broedschroed/NeoChristmasTreeV2/docs/Bilder/20261003_232223.jpg

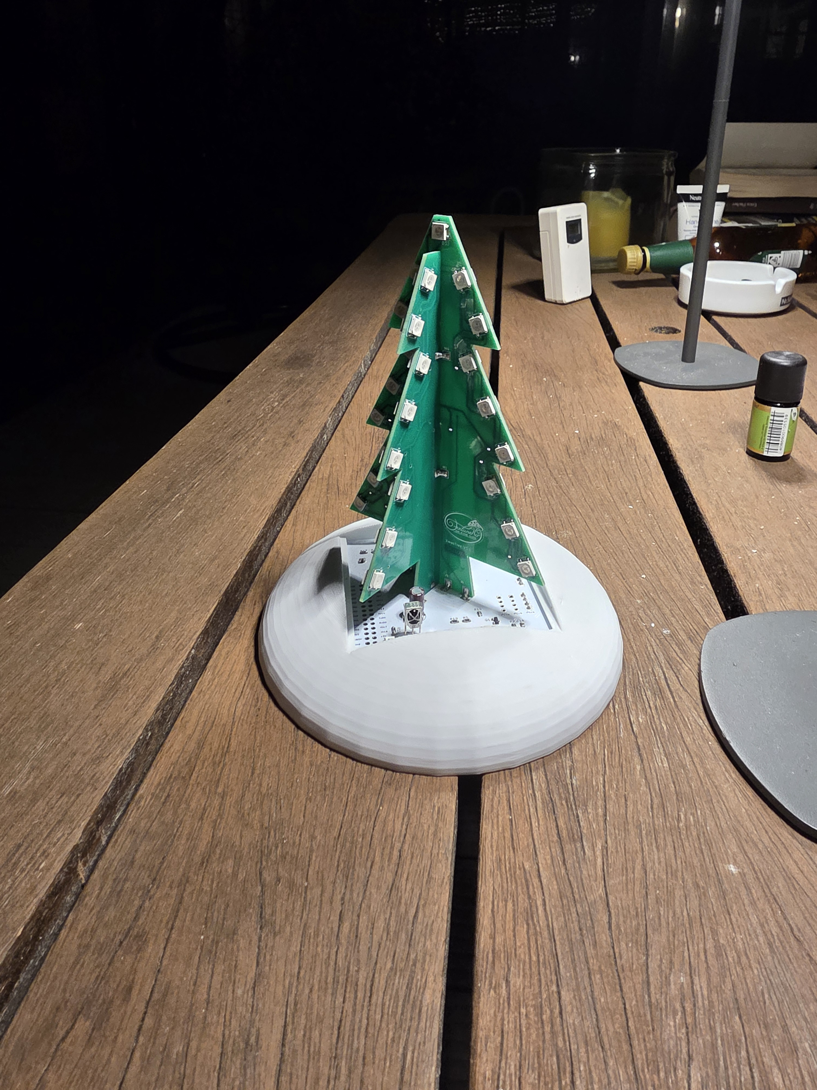
docs/Bilder/20261003_232223.jpg
