broedschroed/NeoChristmasTreeV2/docs/Bilder/20261003_232228.jpg

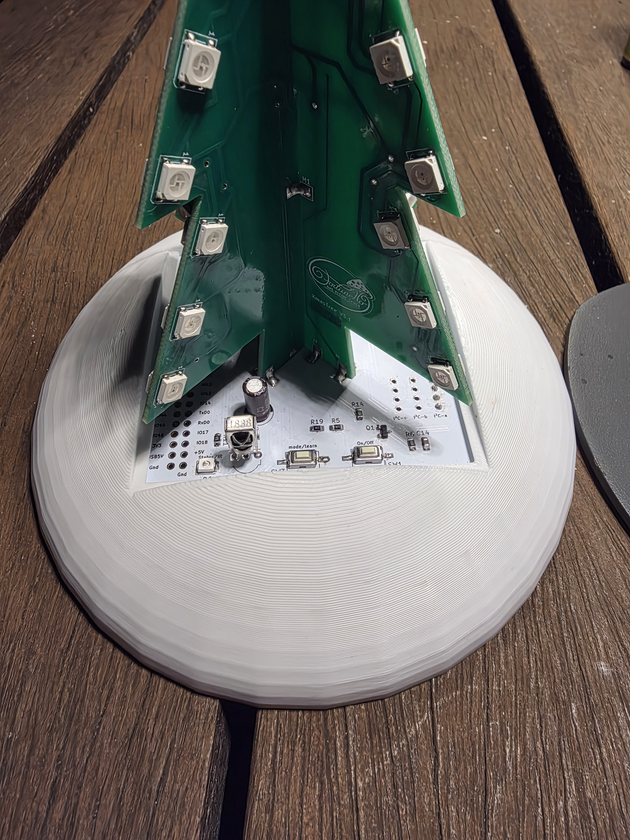
docs/Bilder/20261003_232228.jpg
