broedschroed/NeoChristmasTreeV2/docs/Bilder/20261003_232233.jpg

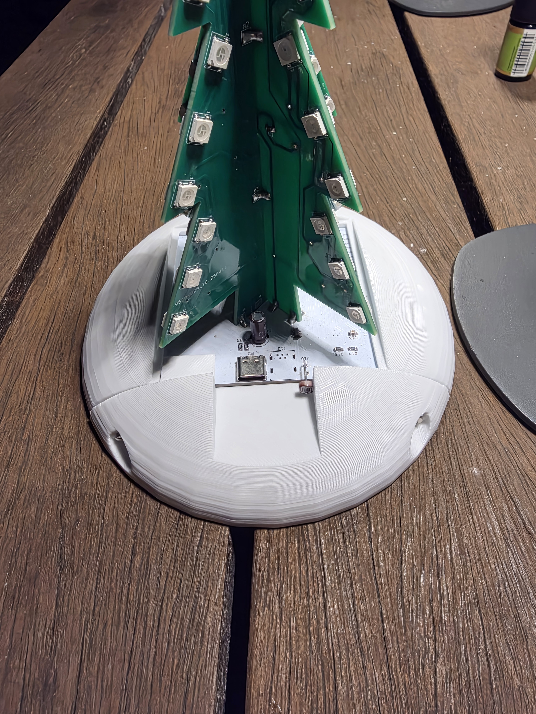
docs/Bilder/20261003_232233.jpg
