broedschroed/NeoChristmasTreeV2/docs/Bilder/20261003_232258.jpg

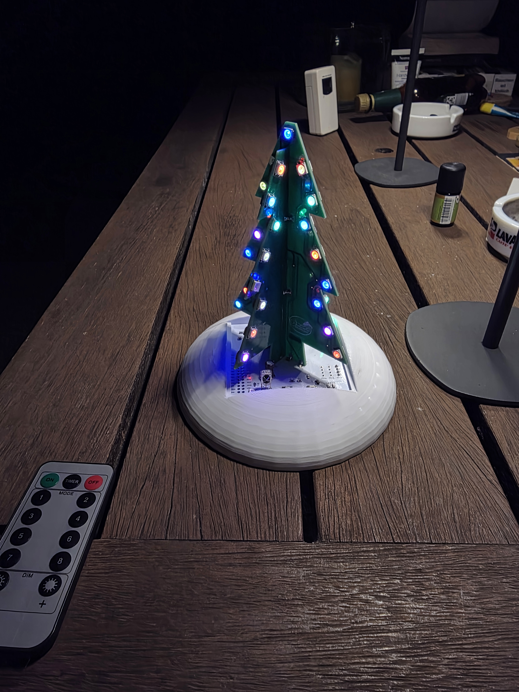
docs/Bilder/20261003_232258.jpg
