broedschroed/NeoChristmasTreeV2/IRcodes.h

#define MAXIRCODES 13

unsigned int defaultIRcodes [MAXIRCODES] = {
  0xFB04FD02,
  0xFA05FD02,
  0xF708FD02,
  0xF609FD02,
  0xF30CFD02,
  0xF20DFD02,
  0xEF10FD02,
  0xEE11FD02,
  0xF906FD02,
  0xF50AFD02,
  0xEB14FD02,
  0xE916FD02,
  0xFE01FD02
};


/*
 * Golden Power Ningbo
 * 
 * ON       = FF00FD02
 * Timer    = FE01FD02
 * OFF      = FD02FD02
 * 1        = FB04FD02
 * 2        = FA05FD02
 * 6H       = F906FD02
 * 3        = F708FD02
 * 4        = F609FD02
 * 8H       = F50AFD02
 * 5        = F30CFD02
 * 6        = F20DFD02
 * 6639H    = F10EFD02
 * 7        = EF10FD02
 * 8        = EE11FD02
 * dark     = EB14FD02
 * light    = E916FD02
 * 
 */
 
