broedschroed/NeoChristmasTreeV2/docs/Bilder/20261003_232220.jpg

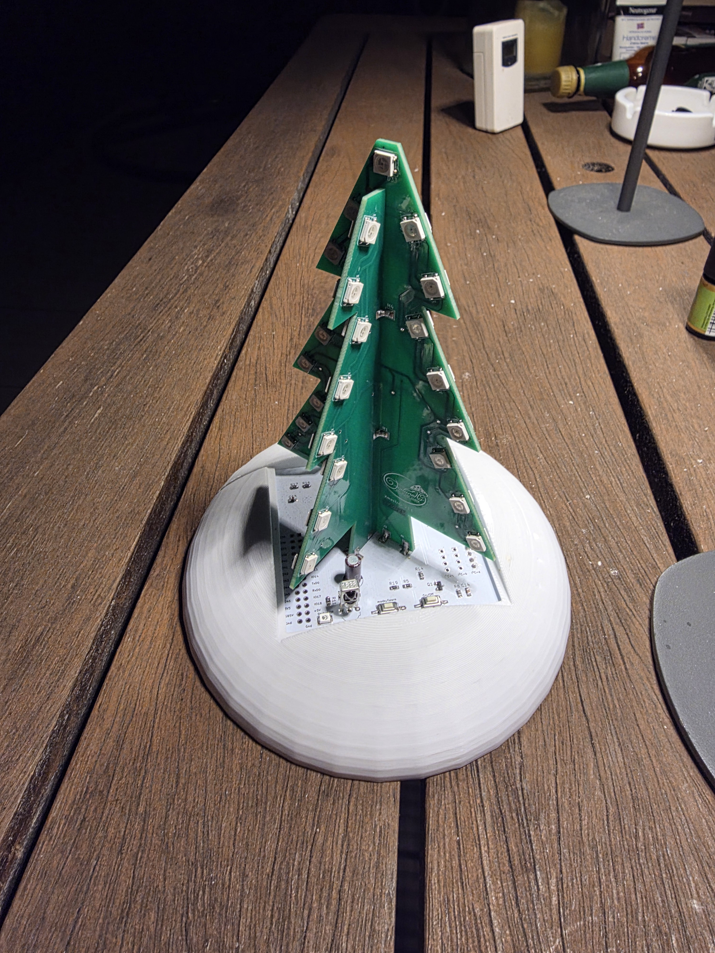
docs/Bilder/20261003_232220.jpg
